namiwijeuom/Sound-Level-Monitoring-System/Enclosure design/Version 3/IMG_20230615_142018_990.jpg

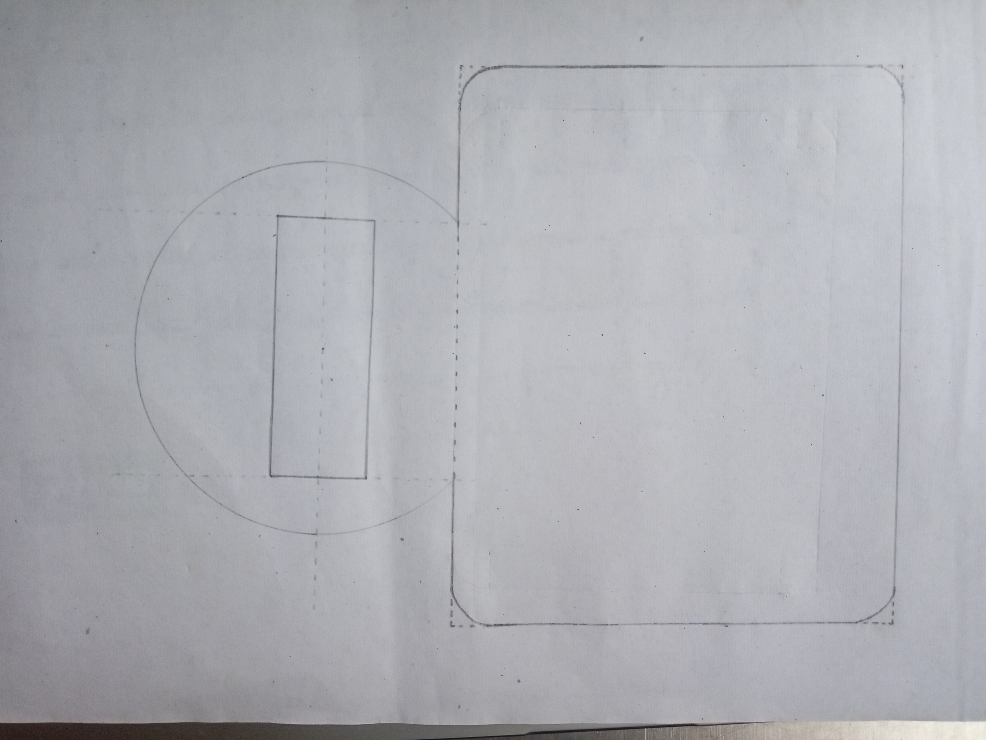
Enclosure design/Version 3/IMG_20230615_142018_990.jpg
