namiwijeuom/Sound-Level-Monitoring-System/Final Evaluation Files/20230716_103215.jpg

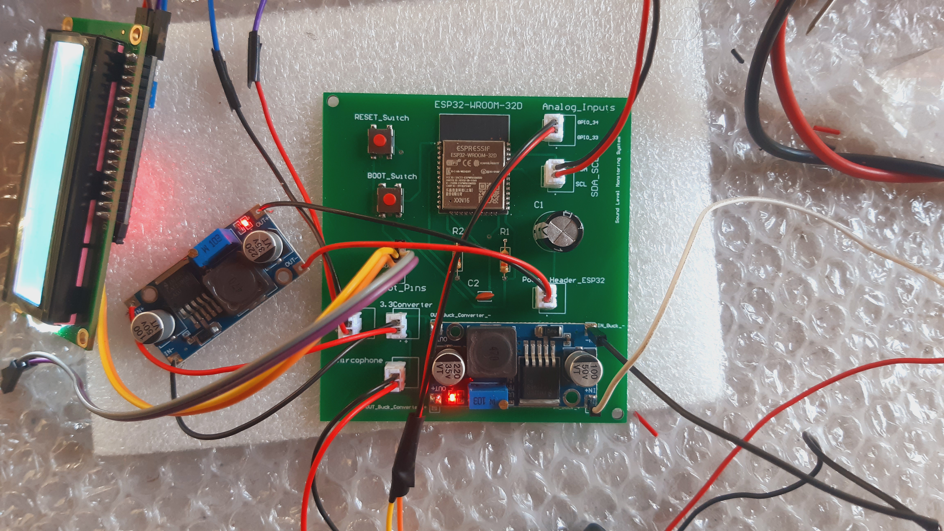
Final Evaluation Files/20230716_103215.jpg
