namiwijeuom/Sound-Level-Monitoring-System/Final Evaluation Files/20230716_141931.jpg

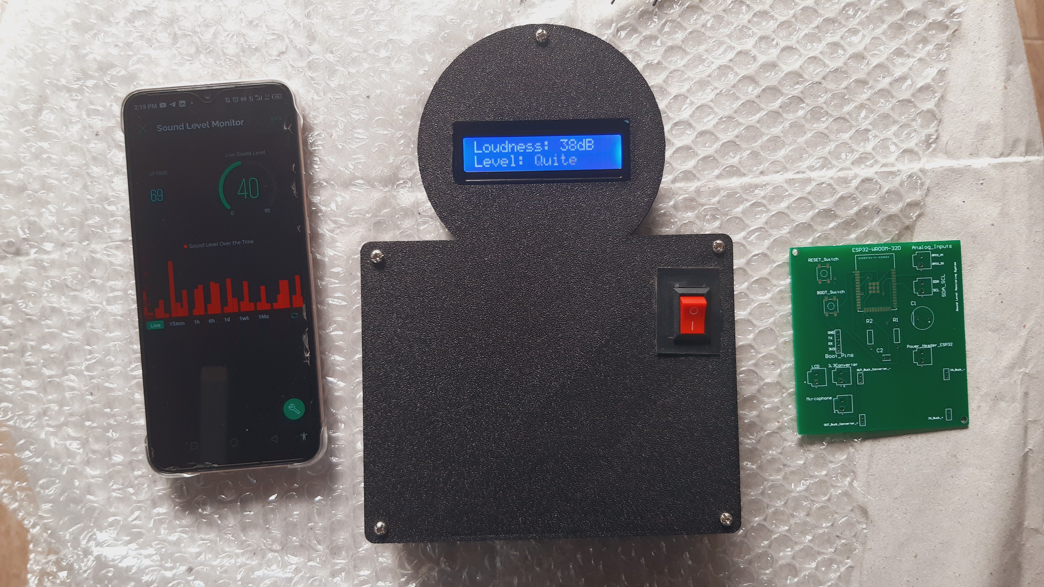
Final Evaluation Files/20230716_141931.jpg
