namiwijeuom/Sound-Level-Monitoring-System/Mid Evaluation Files/IMG_20230610_202826_473.jpg

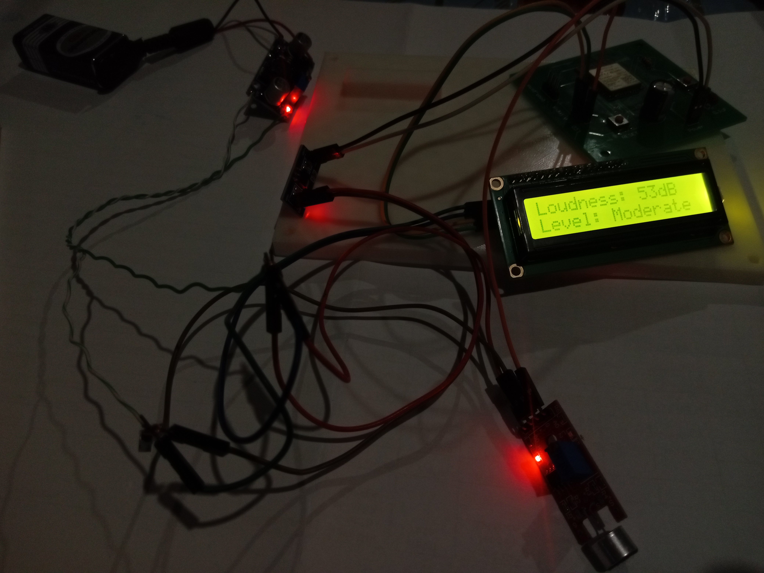
Mid Evaluation Files/IMG_20230610_202826_473.jpg
