namiwijeuom/Sound-Level-Monitoring-System/Mid Evaluation Files/IMG_20230611_140451_065.jpg

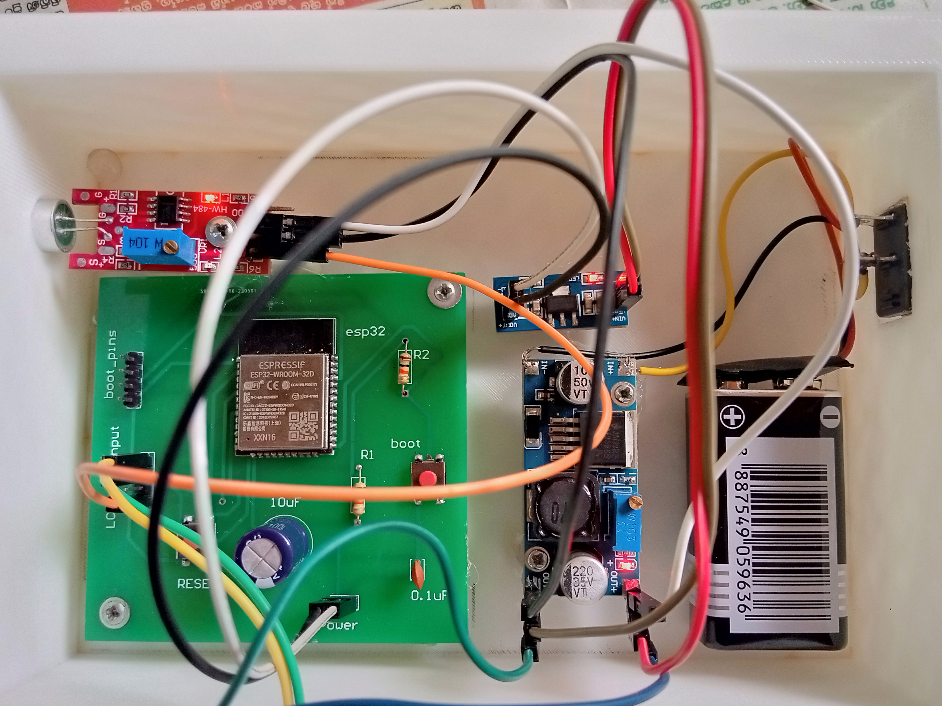
Mid Evaluation Files/IMG_20230611_140451_065.jpg
