namiwijeuom/Sound-Level-Monitoring-System/Mid Evaluation Files/IMG_20230611_140524_982.jpg

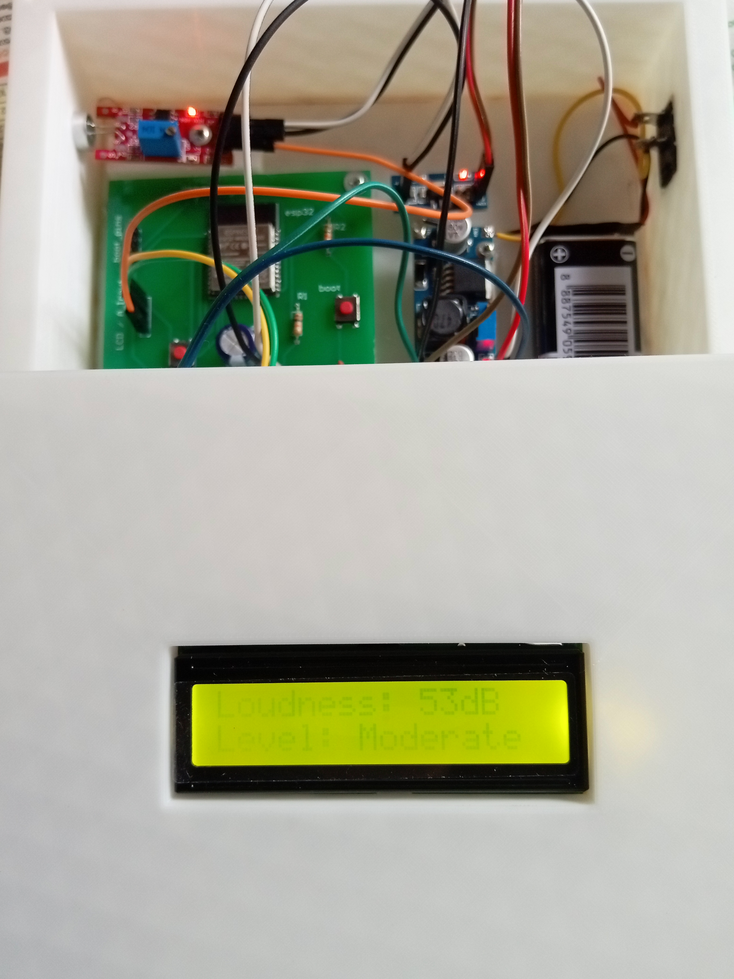
Mid Evaluation Files/IMG_20230611_140524_982.jpg
