namiwijeuom/Sound-Level-Monitoring-System/Final Evaluation Files/20230716_142531.jpg

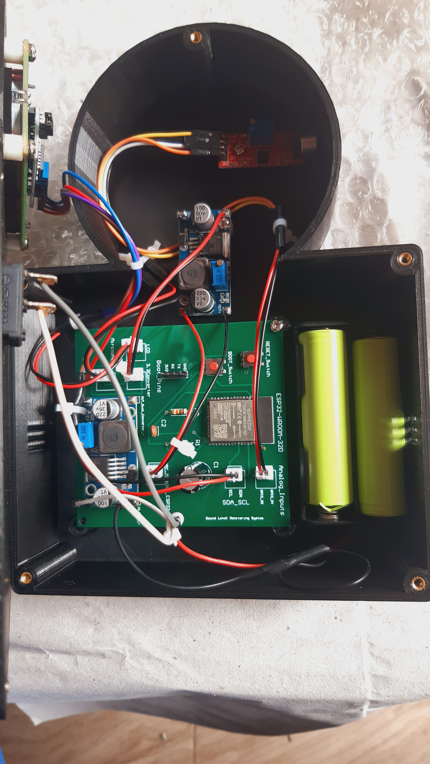
Final Evaluation Files/20230716_142531.jpg
